QArchy/Arbitrary-Waveform-Generator/saw_11.1kHz.png

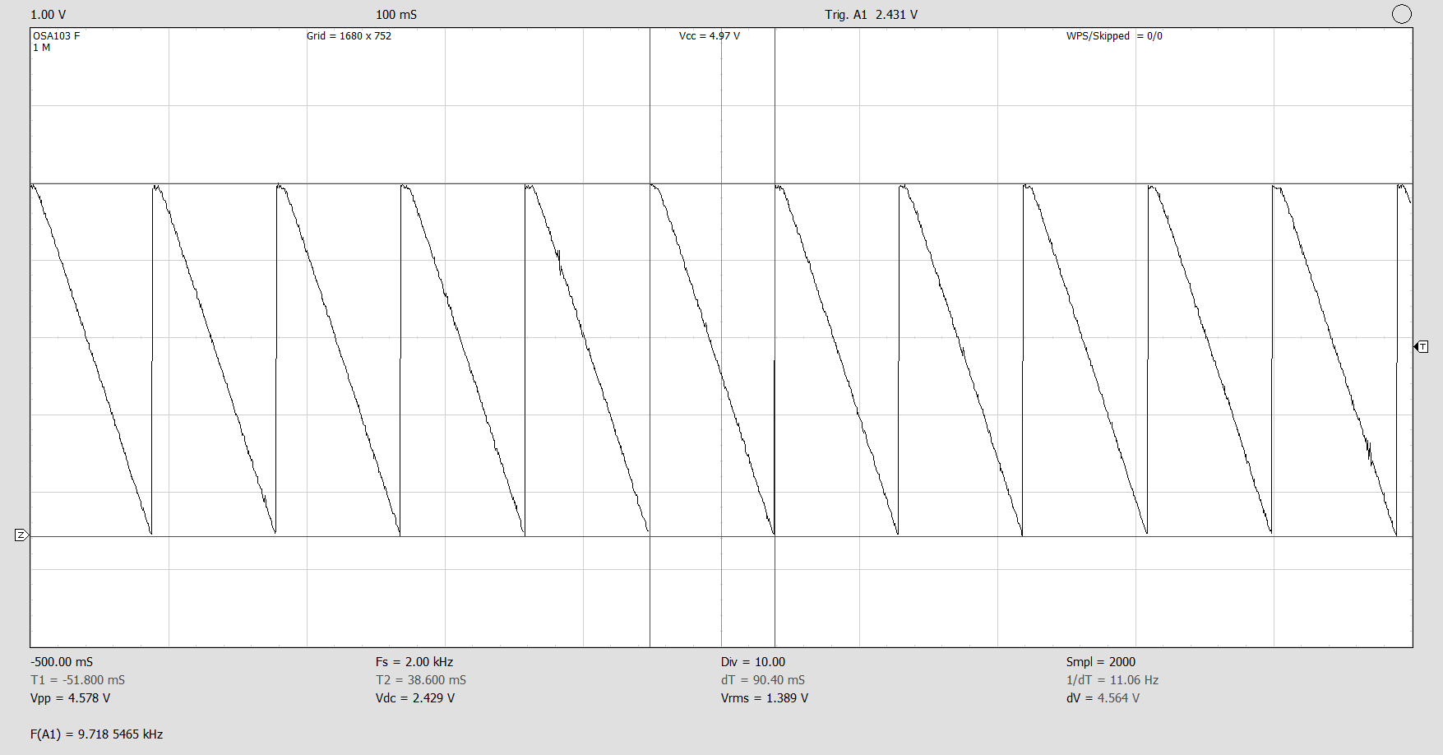
saw_11.1kHz.png
