QArchy/Arbitrary-Waveform-Generator/sin_11.1kHz.png

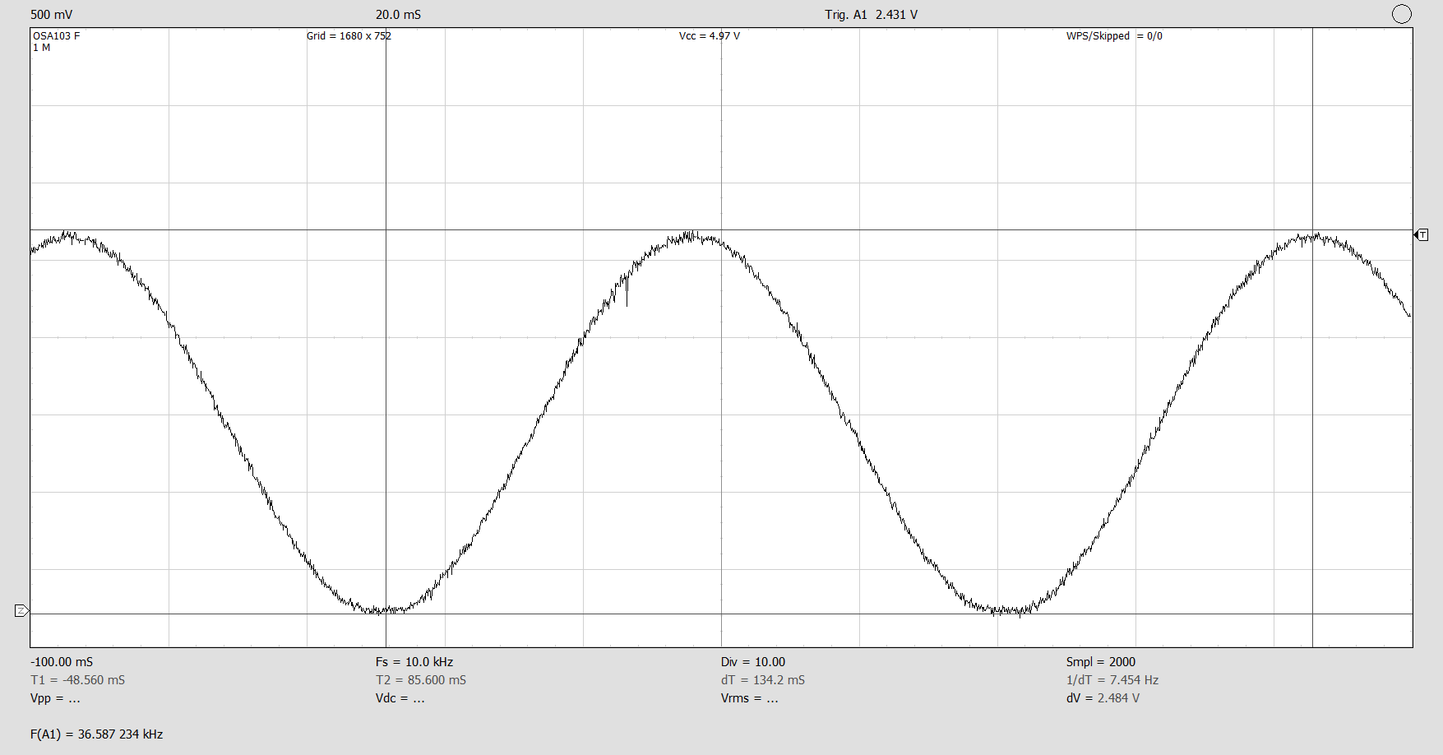
sin_11.1kHz.png
