QArchy/Arbitrary-Waveform-Generator/QuartusProject/project/db/pll_altpll.v

//altpll bandwidth_type="AUTO" CBX_DECLARE_ALL_CONNECTED_PORTS="OFF" clk0_divide_by=125 clk0_duty_cycle=50 clk0_multiply_by=2 clk0_phase_shift="0" clk1_divide_by=5 clk1_duty_cycle=50 clk1_multiply_by=1 clk1_phase_shift="0" clk2_divide_by=1 clk2_duty_cycle=50 clk2_multiply_by=4 clk2_phase_shift="0" compensate_clock="CLK0" device_family="Cyclone IV E" inclk0_input_frequency=20000 intended_device_family="Cyclone IV E" lpm_hint="CBX_MODULE_PREFIX=pll" operation_mode="normal" pll_type="AUTO" port_clk0="PORT_USED" port_clk1="PORT_USED" port_clk2="PORT_USED" port_clk3="PORT_UNUSED" port_clk4="PORT_UNUSED" port_clk5="PORT_UNUSED" port_extclk0="PORT_UNUSED" port_extclk1="PORT_UNUSED" port_extclk2="PORT_UNUSED" port_extclk3="PORT_UNUSED" port_inclk1="PORT_UNUSED" port_phasecounterselect="PORT_UNUSED" port_phasedone="PORT_UNUSED" port_scandata="PORT_UNUSED" port_scandataout="PORT_UNUSED" self_reset_on_loss_lock="OFF" width_clock=5 areset clk inclk locked CARRY_CHAIN="MANUAL" CARRY_CHAIN_LENGTH=48
//VERSION_BEGIN 22.1 cbx_altclkbuf 2023:07:21:07:12:20:SC cbx_altiobuf_bidir 2023:07:21:07:12:21:SC cbx_altiobuf_in 2023:07:21:07:12:21:SC cbx_altiobuf_out 2023:07:21:07:12:21:SC cbx_altpll 2023:07:21:07:12:21:SC cbx_cycloneii 2023:07:21:07:12:21:SC cbx_lpm_add_sub 2023:07:21:07:12:21:SC cbx_lpm_compare 2023:07:21:07:12:21:SC cbx_lpm_counter 2023:07:21:07:12:21:SC cbx_lpm_decode 2023:07:21:07:12:20:SC cbx_lpm_mux 2023:07:21:07:12:21:SC cbx_mgl 2023:07:21:07:12:36:SC cbx_nadder 2023:07:21:07:12:21:SC cbx_stratix 2023:07:21:07:12:21:SC cbx_stratixii 2023:07:21:07:12:21:SC cbx_stratixiii 2023:07:21:07:12:21:SC cbx_stratixv 2023:07:21:07:12:21:SC cbx_util_mgl 2023:07:21:07:12:21:SC  VERSION_END
//CBXI_INSTANCE_NAME="top_pll_pll_inst_altpll_altpll_component"
// synthesis VERILOG_INPUT_VERSION VERILOG_2001
// altera message_off 10463



// Copyright (C) 2023  Intel Corporation. All rights reserved.
//  Your use of Intel Corporation's design tools, logic functions 
//  and other software and tools, and any partner logic 
//  functions, and any output files from any of the foregoing 
//  (including device programming or simulation files), and any 
//  associated documentation or information are expressly subject 
//  to the terms and conditions of the Intel Program License 
//  Subscription Agreement, the Intel Quartus Prime License Agreement,
//  the Intel FPGA IP License Agreement, or other applicable license
//  agreement, including, without limitation, that your use is for
//  the sole purpose of programming logic devices manufactured by
//  Intel and sold by Intel or its authorized distributors.  Please
//  refer to the applicable agreement for further details, at
//  https://fpgasoftware.intel.com/eula.



//synthesis_resources = cycloneive_pll 1 reg 1 
//synopsys translate_off
`timescale 1 ps / 1 ps
//synopsys translate_on
(* ALTERA_ATTRIBUTE = {"SUPPRESS_DA_RULE_INTERNAL=C104;SUPPRESS_DA_RULE_INTERNAL=R101"} *)
module  pll_altpll
	( 
	areset,
	clk,
	inclk,
	locked) /* synthesis synthesis_clearbox=1 */;
	input   areset;
	output   [4:0]  clk;
	input   [1:0]  inclk;
	output   locked;
`ifndef ALTERA_RESERVED_QIS
// synopsys translate_off
`endif
	tri0   areset;
	tri0   [1:0]  inclk;
`ifndef ALTERA_RESERVED_QIS
// synopsys translate_on
`endif

	reg	pll_lock_sync;
	wire  [4:0]   wire_pll1_clk;
	wire  wire_pll1_fbout;
	wire  wire_pll1_locked;

	// synopsys translate_off
	initial
		pll_lock_sync = 0;
	// synopsys translate_on
	always @ ( posedge wire_pll1_locked or  posedge areset)
		if (areset == 1'b1) pll_lock_sync <= 1'b0;
		else  pll_lock_sync <= 1'b1;
	cycloneive_pll   pll1
	( 
	.activeclock(),
	.areset(areset),
	.clk(wire_pll1_clk),
	.clkbad(),
	.fbin(wire_pll1_fbout),
	.fbout(wire_pll1_fbout),
	.inclk(inclk),
	.locked(wire_pll1_locked),
	.phasedone(),
	.scandataout(),
	.scandone(),
	.vcooverrange(),
	.vcounderrange()
	`ifndef FORMAL_VERIFICATION
	// synopsys translate_off
	`endif
	,
	.clkswitch(1'b0),
	.configupdate(1'b0),
	.pfdena(1'b1),
	.phasecounterselect({3{1'b0}}),
	.phasestep(1'b0),
	.phaseupdown(1'b0),
	.scanclk(1'b0),
	.scanclkena(1'b1),
	.scandata(1'b0)
	`ifndef FORMAL_VERIFICATION
	// synopsys translate_on
	`endif
	);
	defparam
		pll1.bandwidth_type = "auto",
		pll1.clk0_divide_by = 125,
		pll1.clk0_duty_cycle = 50,
		pll1.clk0_multiply_by = 2,
		pll1.clk0_phase_shift = "0",
		pll1.clk1_divide_by = 5,
		pll1.clk1_duty_cycle = 50,
		pll1.clk1_multiply_by = 1,
		pll1.clk1_phase_shift = "0",
		pll1.clk2_divide_by = 1,
		pll1.clk2_duty_cycle = 50,
		pll1.clk2_multiply_by = 4,
		pll1.clk2_phase_shift = "0",
		pll1.compensate_clock = "clk0",
		pll1.inclk0_input_frequency = 20000,
		pll1.operation_mode = "normal",
		pll1.pll_type = "auto",
		pll1.self_reset_on_loss_lock = "off",
		pll1.lpm_type = "cycloneive_pll";
	assign
		clk = {wire_pll1_clk[4:0]},
		locked = (wire_pll1_locked & pll_lock_sync);
endmodule //pll_altpll
//VALID FILE
